mhuot/mini-rack-laptop-trays/exports/print_plate_duct_panels.3mf

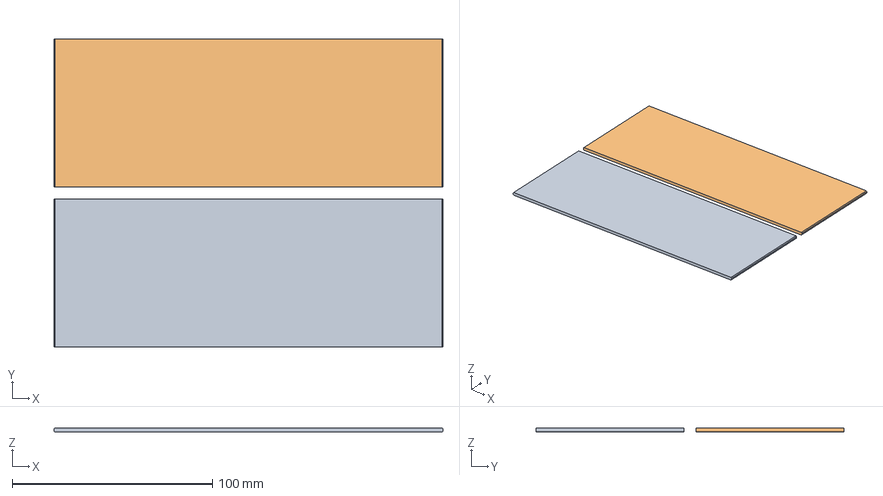
[picture p22: CAD file, 2026-08-26]
exports/print_plate_duct_panels.3mf
194.4 x 154.0 x 2.20 mm
duct_panel_top
duct_panel_bottom
