mhuot/mini-rack-laptop-trays/exports/print_plate_ears_nuttrap.3mf

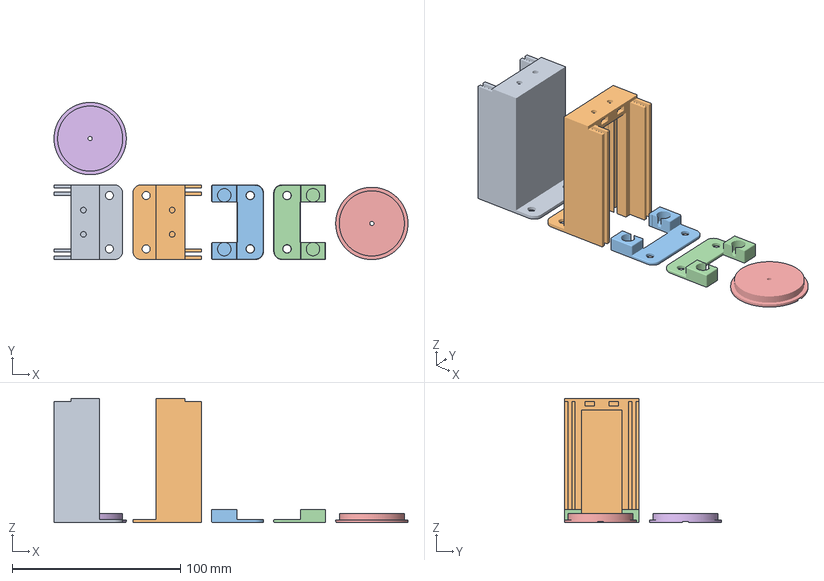
[picture p23: CAD file, 2026-08-26]
exports/print_plate_ears_nuttrap.3mf
210.5 x 93.4 x 74.0 mm
rear_ear_R
rear_ear_L
front_ear_R
front_ear_L
fan_plug_1
fan_plug_2
